smooker/scales_stepper_stm32/src/main_an2594.c

/**
  ******************************************************************************
  * @file    EEPROM_Emulation/src/main.c 
  * @author  MCD Application Team
  * @version V3.1.0
  * @date    07/27/2009
  * @brief   Main program body
  ******************************************************************************
  * @copy
  *
  * THE PRESENT FIRMWARE WHICH IS FOR GUIDANCE ONLY AIMS AT PROVIDING CUSTOMERS
  * WITH CODING INFORMATION REGARDING THEIR PRODUCTS IN ORDER FOR THEM TO SAVE
  * TIME. AS A RESULT, STMICROELECTRONICS SHALL NOT BE HELD LIABLE FOR ANY
  * DIRECT, INDIRECT OR CONSEQUENTIAL DAMAGES WITH RESPECT TO ANY CLAIMS ARISING
  * FROM THE CONTENT OF SUCH FIRMWARE AND/OR THE USE MADE BY CUSTOMERS OF THE
  * CODING INFORMATION CONTAINED HEREIN IN CONNECTION WITH THEIR PRODUCTS.
  *
  * <h2><center>&copy; COPYRIGHT 2009 STMicroelectronics</center></h2>
  */ 

/** @addtogroup EEPROM_Emulation
  * @{
  */ 

/* Includes ------------------------------------------------------------------*/
#include "eeprom.h"

/* Private typedef -----------------------------------------------------------*/
/* Private define ------------------------------------------------------------*/
/* Private macro -------------------------------------------------------------*/
/* Private variables ---------------------------------------------------------*/
ErrorStatus  HSEStartUpStatus;
FLASH_Status FlashStatus;
uint16_t VarValue = 0;

/* Virtual address defined by the user: 0xFFFF value is prohibited */
uint16_t VirtAddVarTab[NumbOfVar] = {0x5555, 0x6666, 0x7777};

/* Private function prototypes -----------------------------------------------*/
/* Private functions ---------------------------------------------------------*/

/**
  * @brief  Main program.
  * @param  None
  * @retval None
  */
int main(void)
{
  /* Setup STM32 system (clock, PLL and Flash configuration) */
  SystemInit();

  /* Unlock the Flash Program Erase controller */
  FLASH_Unlock();

  /* EEPROM Init */
  EE_Init();

/* --- Store successively many values of the three variables in the EEPROM ---*/
  /* Store 1000 values of Variable1 in EEPROM */
  for (VarValue = 0; VarValue < 1000; VarValue++)
  {
    EE_WriteVariable(VirtAddVarTab[0], VarValue);
  }

  /* Store 500 values of Variable2 in EEPROM */
  for (VarValue = 0; VarValue < 500; VarValue++)
  {
    EE_WriteVariable(VirtAddVarTab[1], VarValue);
  }

  /* Store 800 values of Variable3 in EEPROM */
  for (VarValue = 0; VarValue < 800; VarValue++)
  {
    EE_WriteVariable(VirtAddVarTab[2], VarValue);
  }

  while (1);
}

#ifdef USE_FULL_ASSERT
/**
  * @brief  Reports the name of the source file and the source line number
  *   where the assert_param error has occurred.
  * @param file: pointer to the source file name
  * @param line: assert_param error line source number
  * @retval None
  */
void assert_failed(uint8_t* file, uint32_t line)
{
  /* User can add his own implementation to report the file name and line number,
     ex: printf("Wrong parameters value: file %s on line %d\r\n", file, line) */

  /* Infinite loop */
  while (1)
  {}
}
#endif

/**
  * @}
  */ 

/******************* (C) COPYRIGHT 2009 STMicroelectronics *****END OF FILE****/
